Okarisu/Divergence-Meter/src/main/byte_lib.h

//
// Created by Toohka on 17.06.2022.
//

#ifndef SRC_BYTE_LIB_H
#define SRC_BYTE_LIB_H

//DIGITS
#define sym0 B00000011
#define sym1 B10011111
#define sym2 B00100101
#define sym3 B00001101
#define sym4 B10110001
#define sym5 B01001001
#define sym6 B01000001
#define sym7 B00011111
#define sym8 B00000001
#define sym9 B00001001

//SYMBOLS
#define symDot B11111110
#define symStroke B11111101

//GRIDS
#define grid1 B01111111
#define grid2 B10111111
#define grid3 B11011111
#define grid4 B11101111
#define grid5 B11110111
#define grid6 B11111011
#define grid7 B11111101
#define grid8 B11111110


#endif //SRC_BYTE_LIB_H
