Okarisu/Divergence-Meter/src/main/matrix.h

//
// Created by Toohka on 01.06.2022.
//
#include "byte_lib.h"

#ifndef SRC_MATRIX_H
#define SRC_MATRIX_H

byte matrix[10] {sym0, sym1, sym2, sym3, sym4, sym5, sym6, sym7, sym8, sym9};

#endif //SRC_MATRIX_H
